syk-yaman/lora-mesh/Code/Current Analysis/deepsleep-spike-zoomed.png

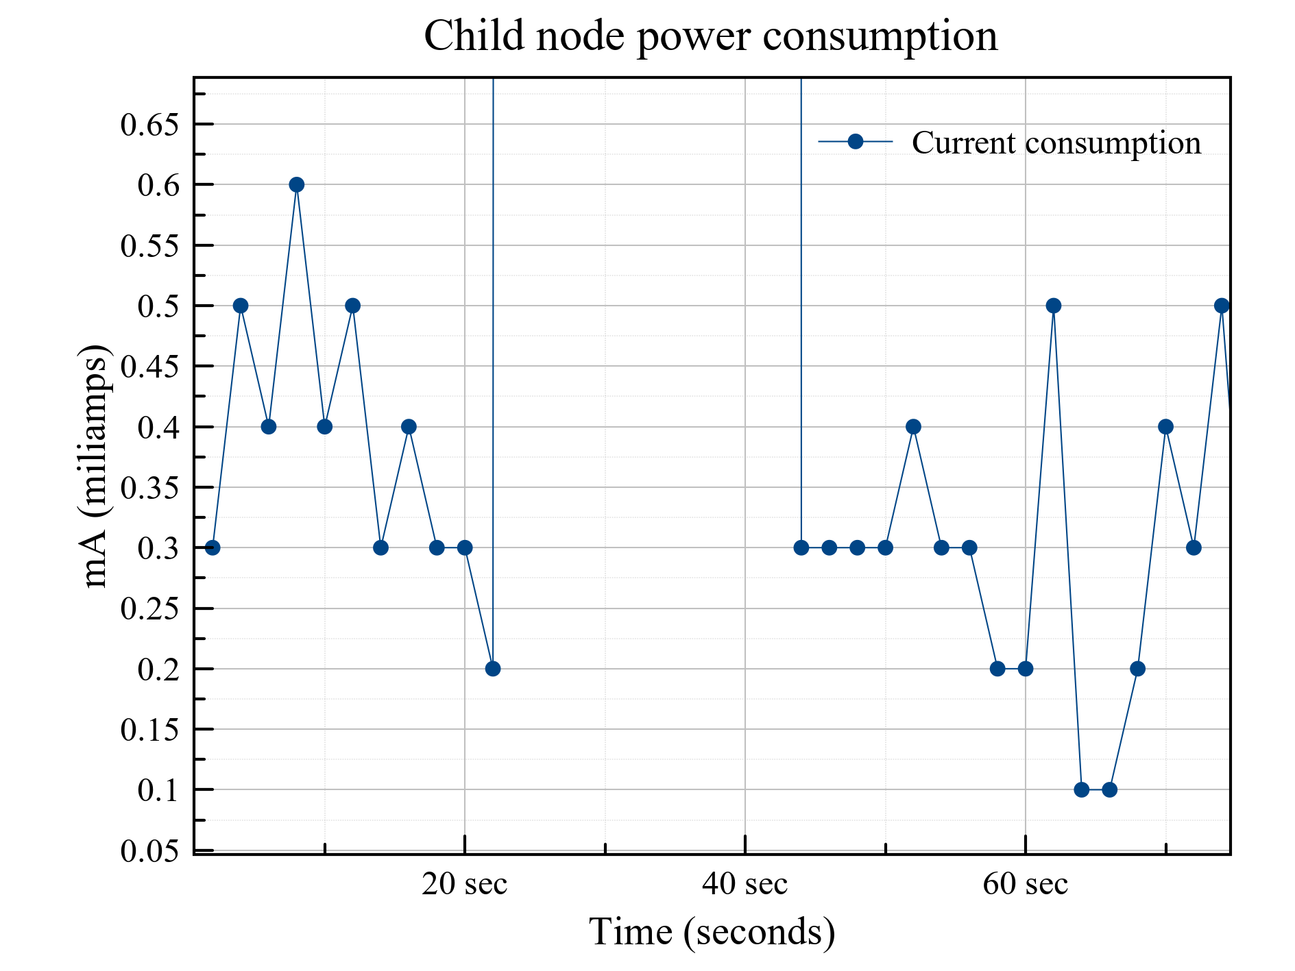
Code/Current Analysis/deepsleep-spike-zoomed.png
