syk-yaman/lora-mesh/Code/Current Analysis/router-node-booting.png

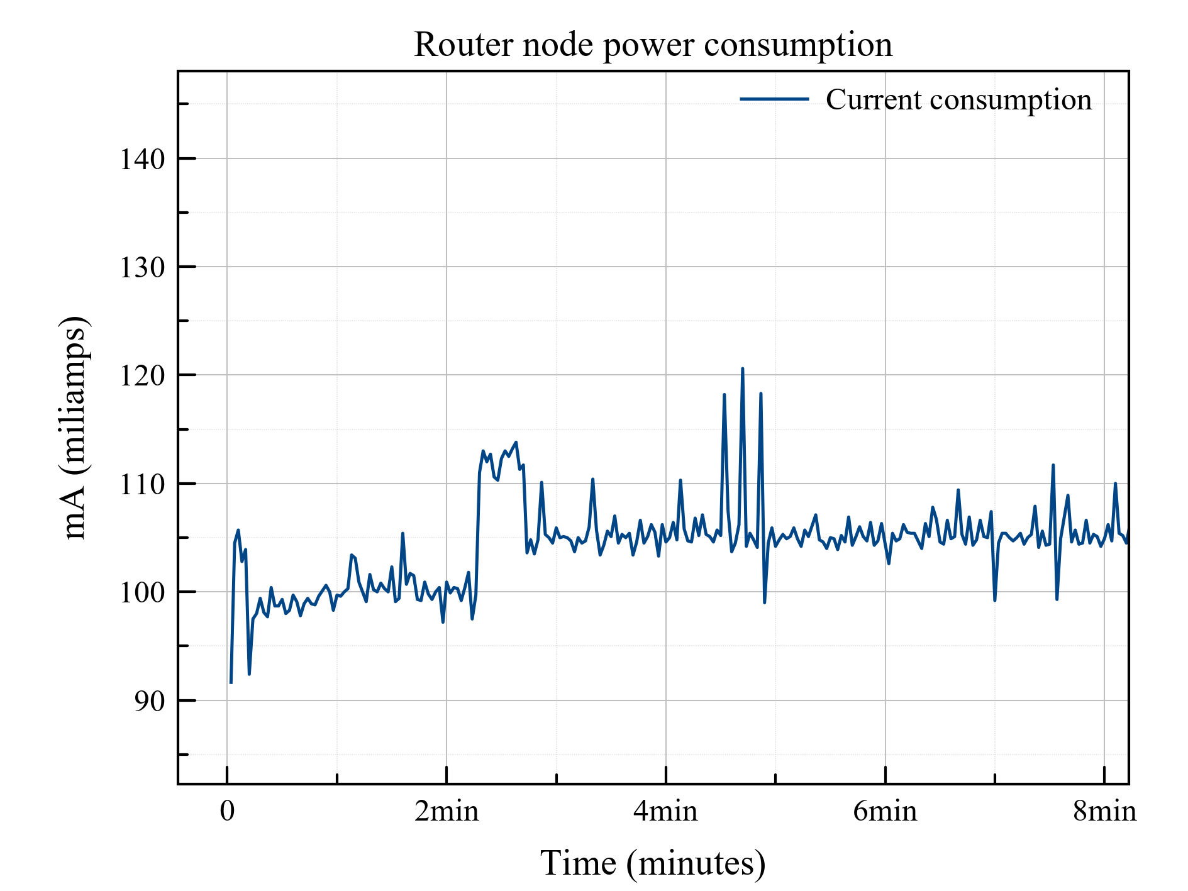
Code/Current Analysis/router-node-booting.png
