syk-yaman/lora-mesh/Code/DataTable/BaseMap.jpg

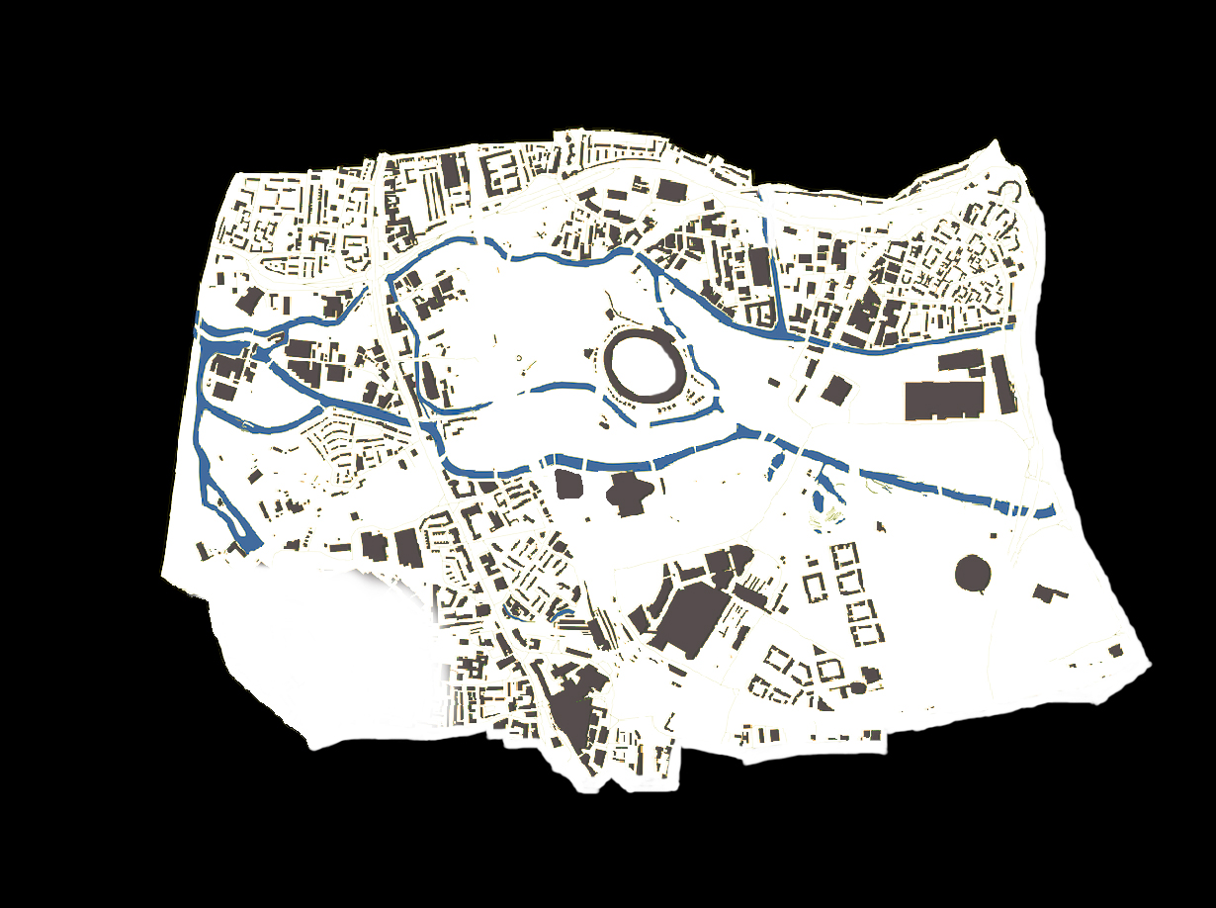
Code/DataTable/BaseMap.jpg
