syk-yaman/lora-mesh/Code/DataTable/TopographicMap.jpg

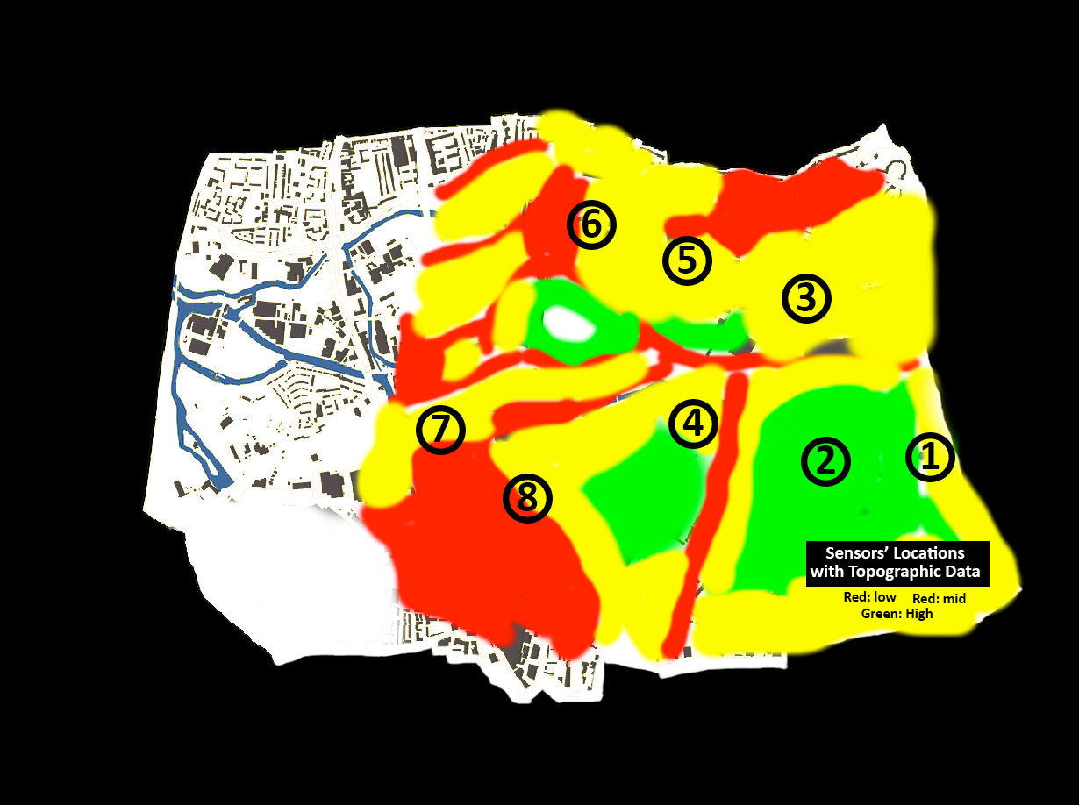
Code/DataTable/TopographicMap.jpg
