syk-yaman/lora-mesh/Docs/images/deployed-mesh-1.jpg

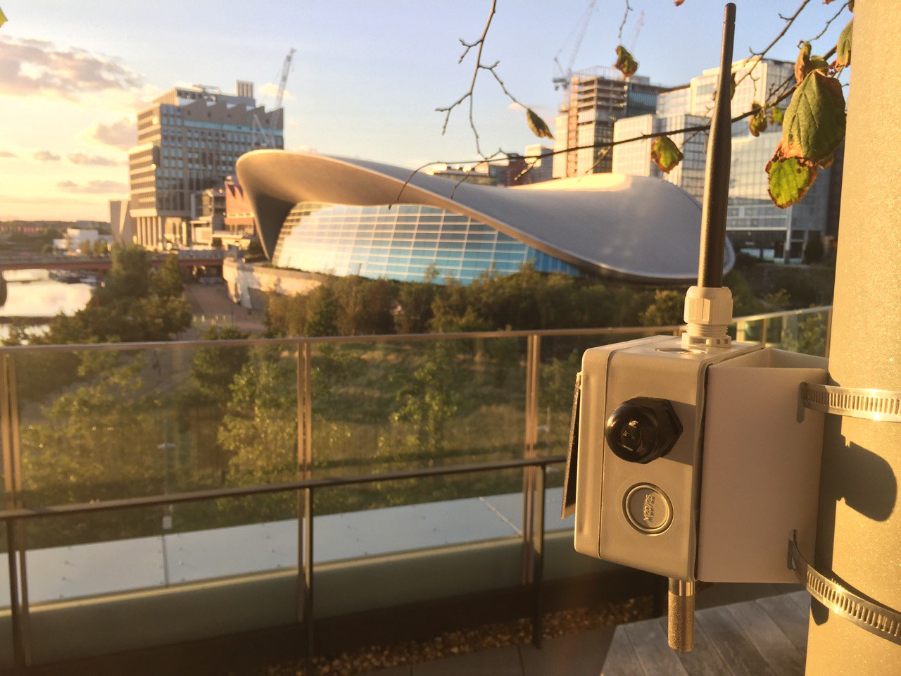
Docs/images/deployed-mesh-1.jpg
