syk-yaman/lora-mesh/Experiments/Experiment4/Deployment plan/OPS-3.jpg

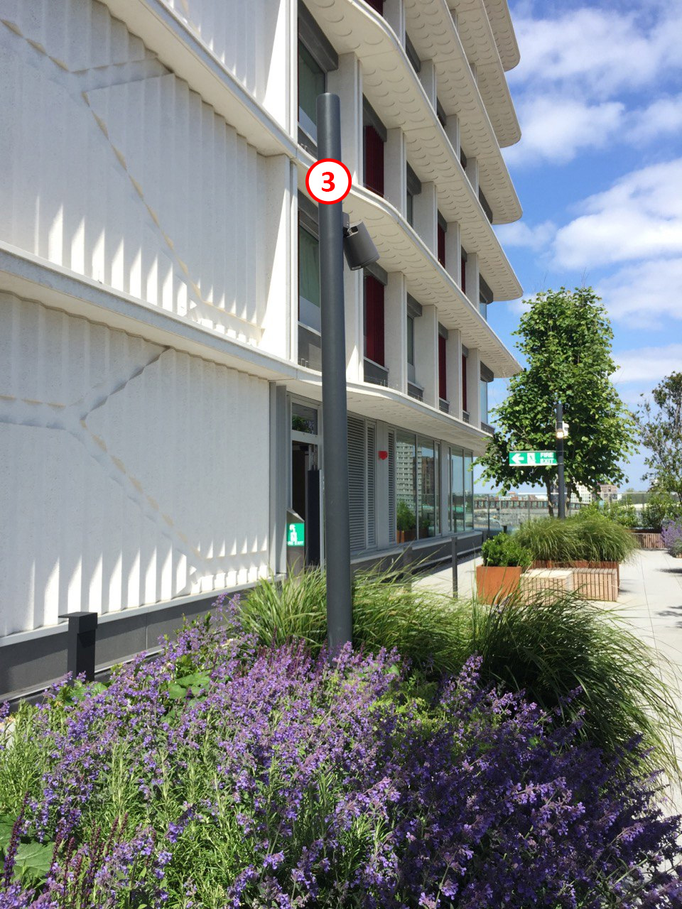
Experiments/Experiment4/Deployment plan/OPS-3.jpg
