syk-yaman/lora-mesh/Experiments/Experiment4/Deployment plan/Topographic-map.jpg

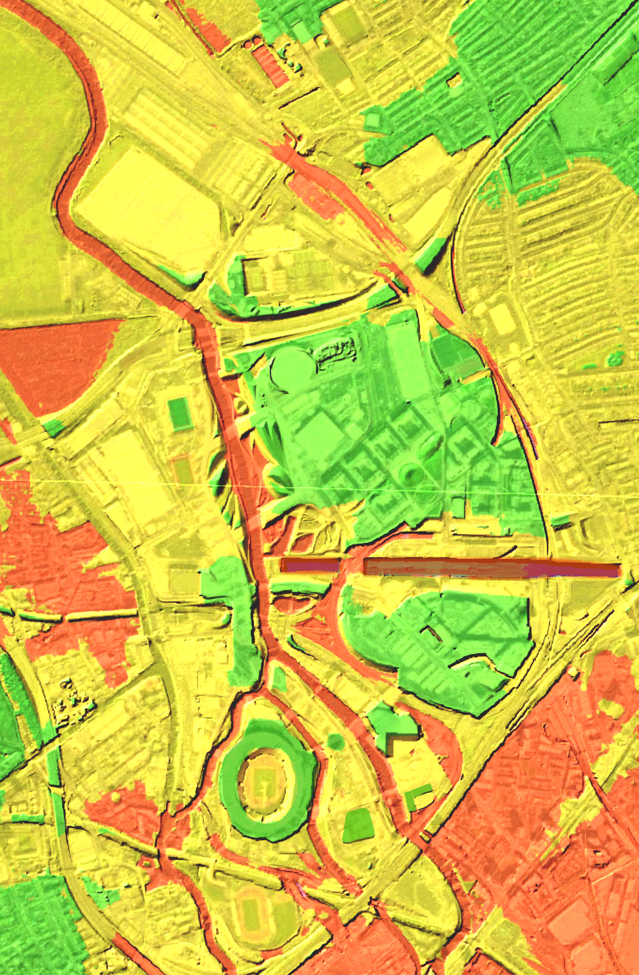
Experiments/Experiment4/Deployment plan/Topographic-map.jpg
